epatel/my_voron/images/voron/IMG_20221023_183006.jpg

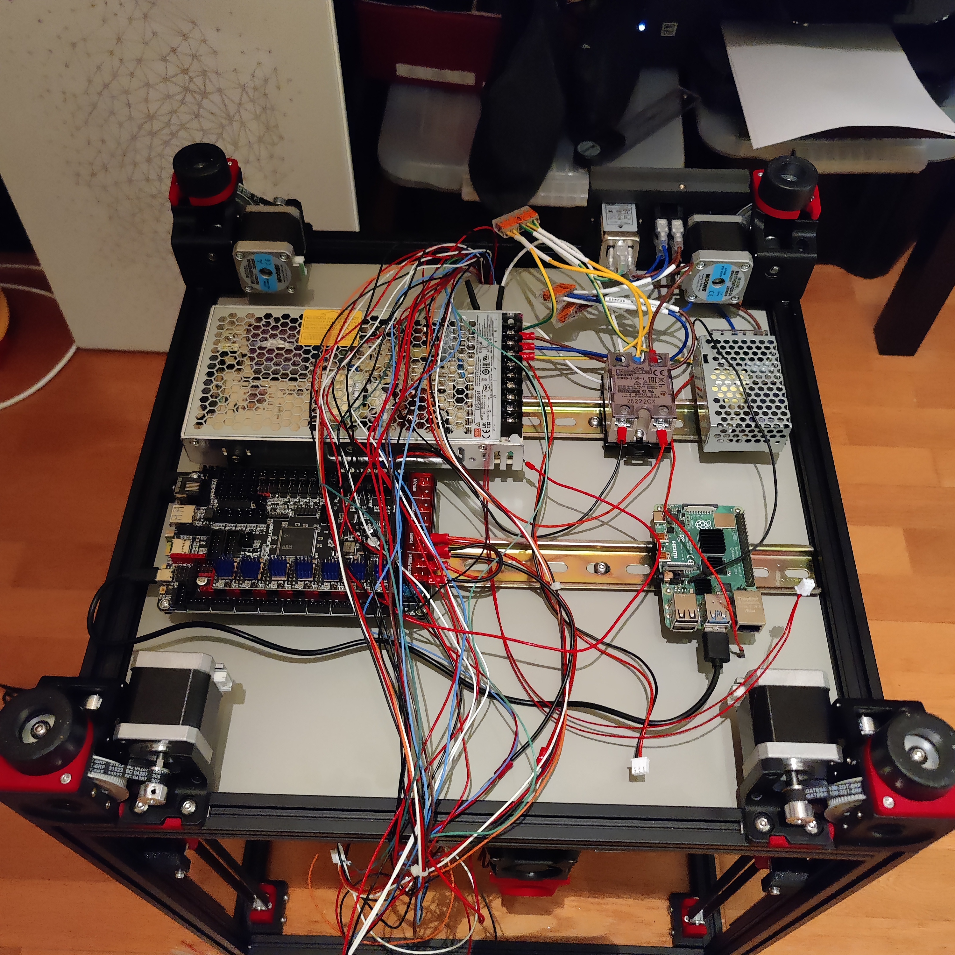
images/voron/IMG_20221023_183006.jpg
