epatel/my_voron/images/voron/IMG_20221022_132712.jpg

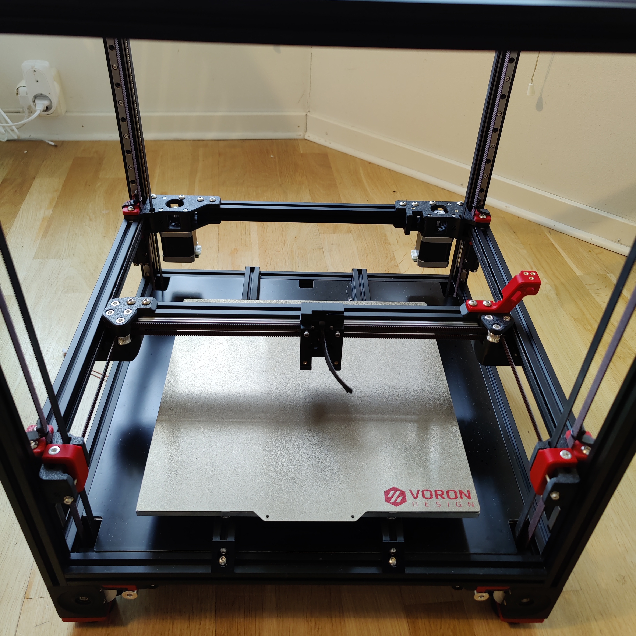
images/voron/IMG_20221022_132712.jpg
