epatel/my_voron/images/minivoron/IMG_20230226_104324.jpg

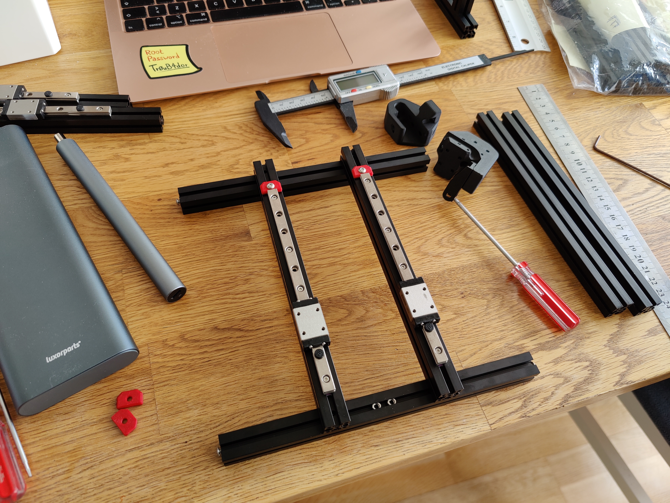
images/minivoron/IMG_20230226_104324.jpg
