epatel/my_voron/images/minivoron/IMG_20230226_104353.jpg

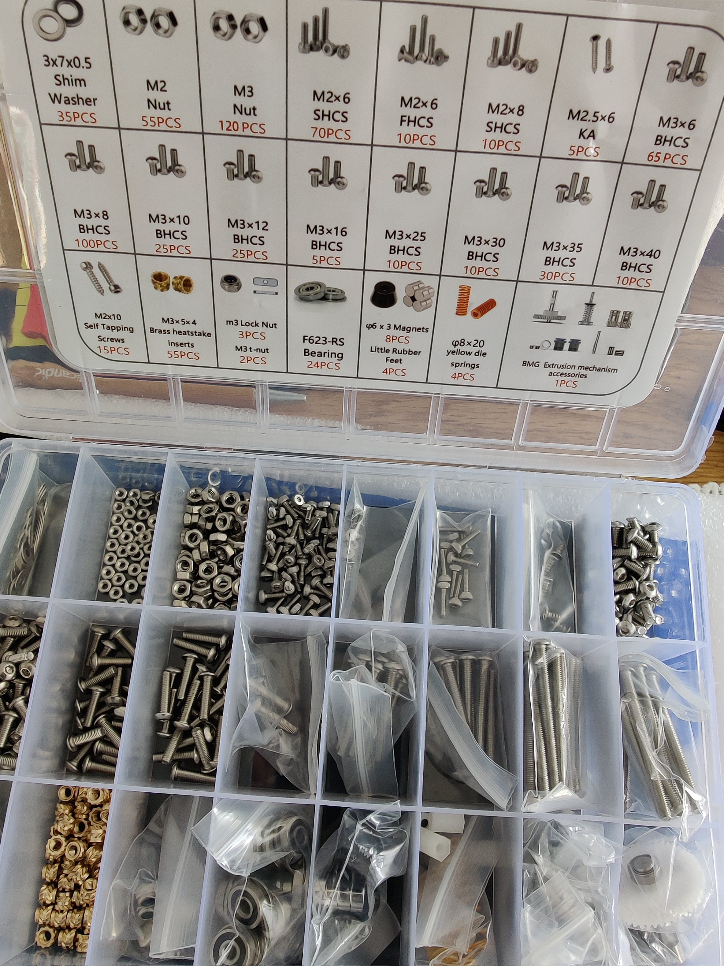
images/minivoron/IMG_20230226_104353.jpg
