epatel/my_voron/images/minivoron/IMG_20230226_121627.jpg

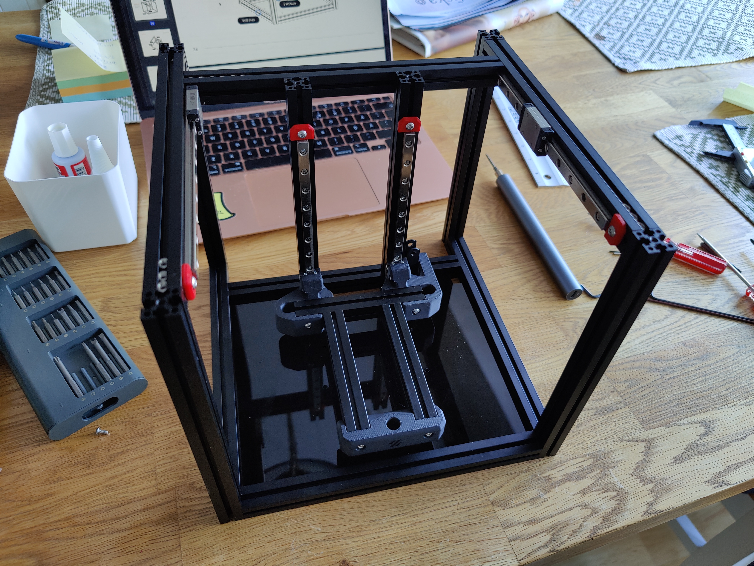
images/minivoron/IMG_20230226_121627.jpg
