epatel/my_voron/images/minivoron/IMG_20230226_133033.jpg

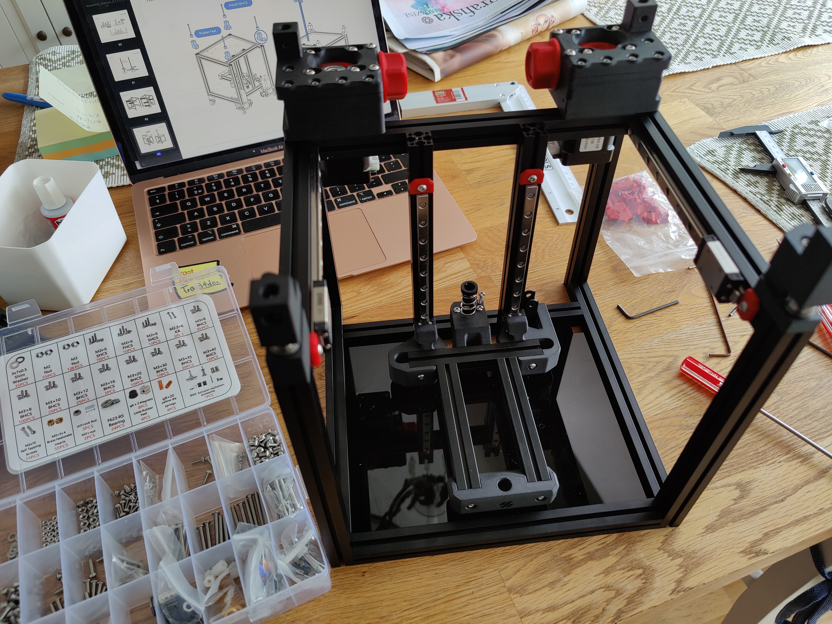
images/minivoron/IMG_20230226_133033.jpg
