epatel/my_voron/images/minivoron/IMG_20230226_171731.jpg

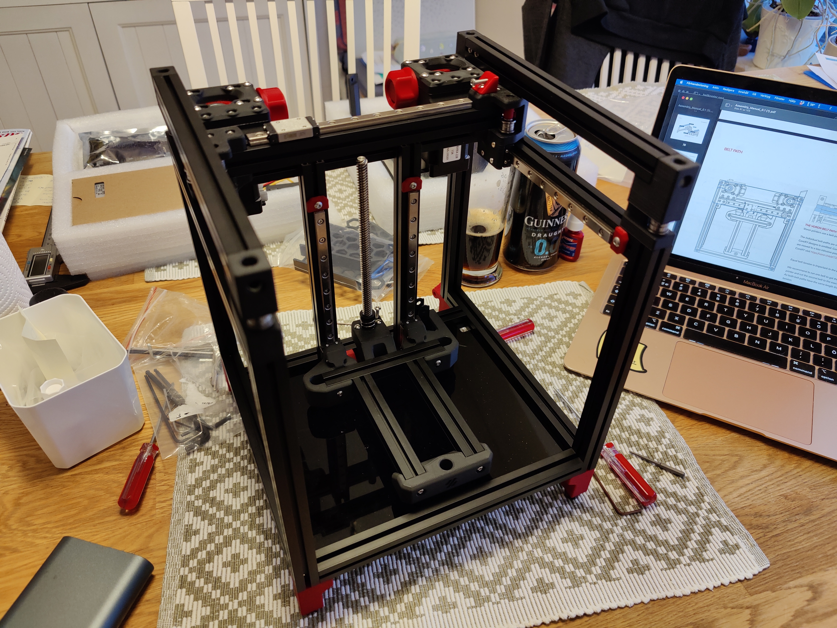
images/minivoron/IMG_20230226_171731.jpg
