epatel/my_voron/images/voron/IMG_20221016_122122.jpg

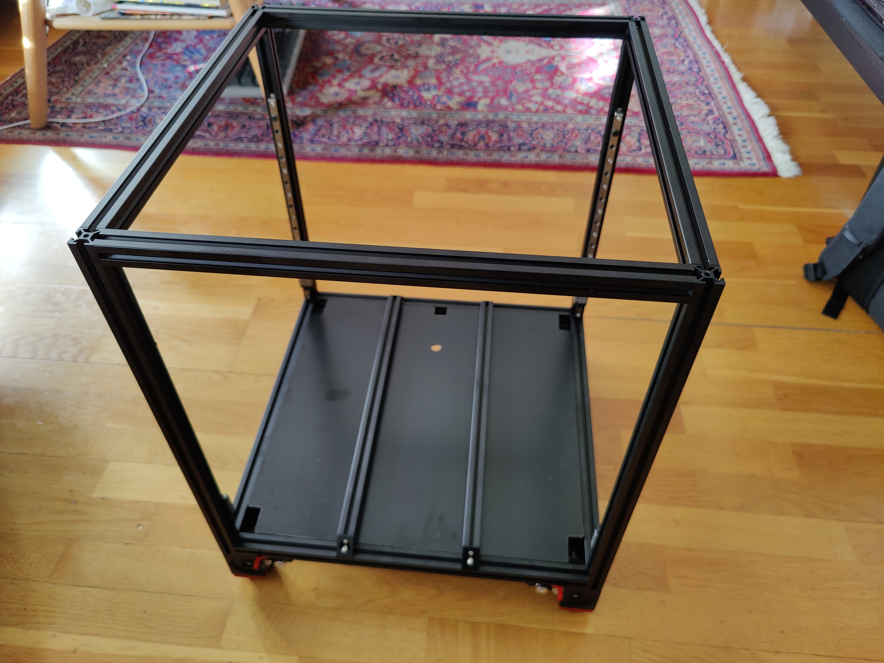
images/voron/IMG_20221016_122122.jpg
