epatel/my_voron/images/voron/IMG_20221023_130440.jpg

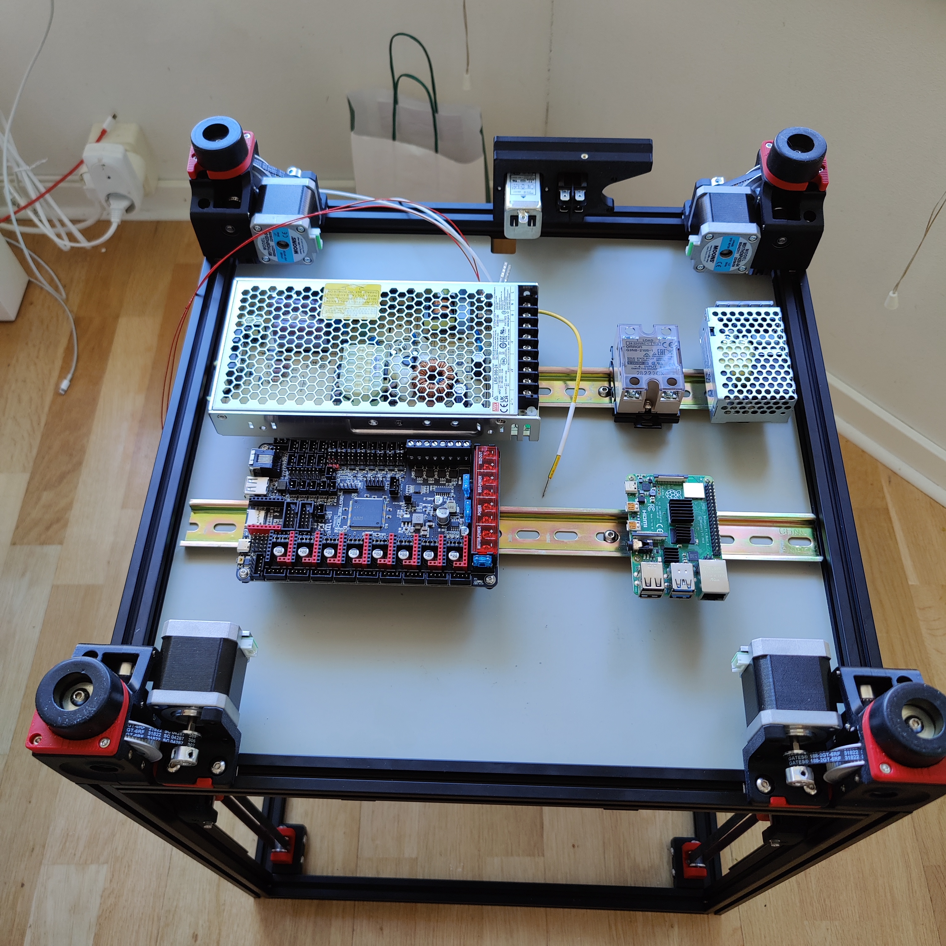
images/voron/IMG_20221023_130440.jpg
