epatel/my_voron/images/voron/IMG_20221023_182126.jpg

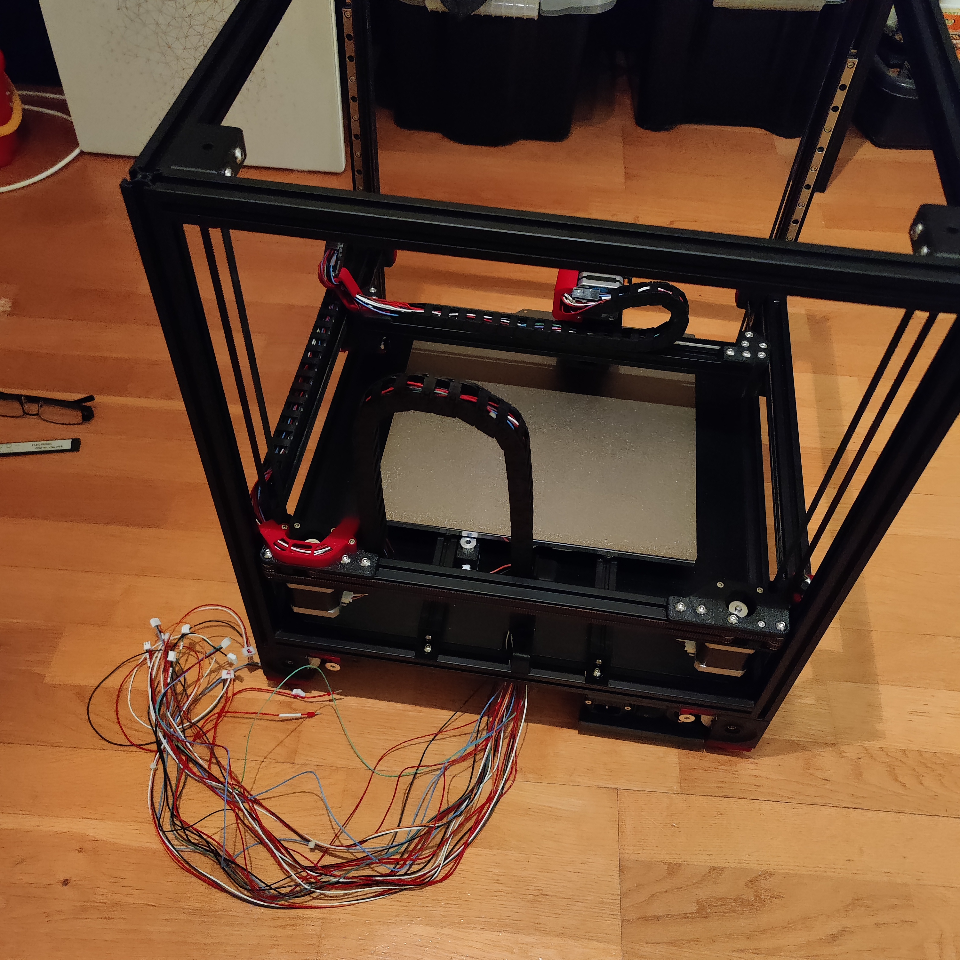
images/voron/IMG_20221023_182126.jpg
