epatel/my_voron/images/voron/IMG_20221025_175646.jpg

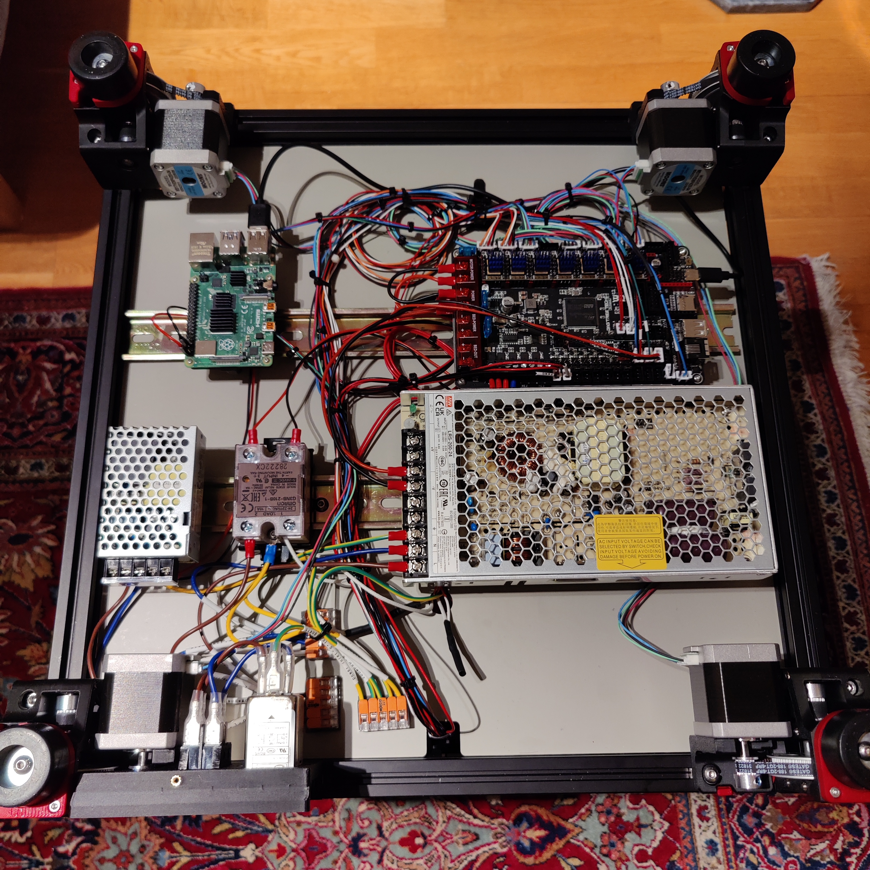
images/voron/IMG_20221025_175646.jpg
