epatel/my_voron/images/voron/IMG_20221030_110302.jpg

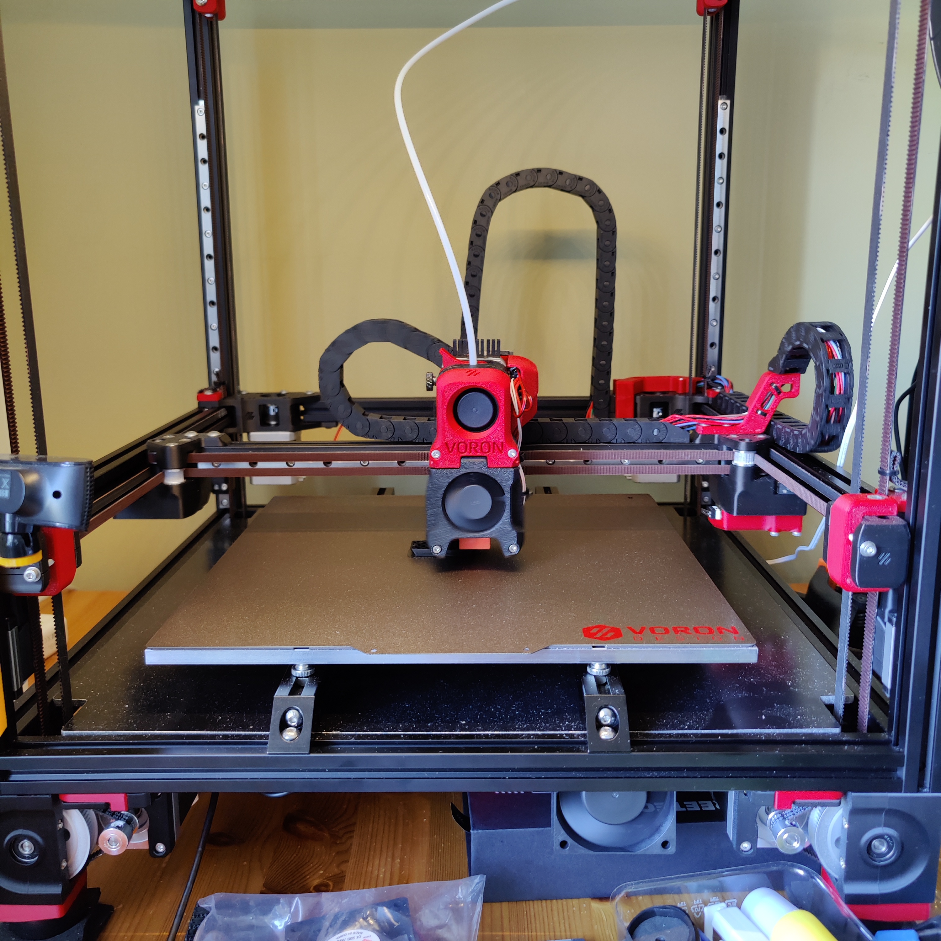
images/voron/IMG_20221030_110302.jpg
